ultimaterobotics/uEMG/uEMG_v3/bmi160.h

#include "nrf.h"
#include "nrf_gpio.h"
#include <stdint.h>

typedef struct sBMI160
{
	uint32_t CS;
	float rawA2SI;
	float rawG2SI;
	
	float aX;
	float aY;
	float aZ;

	float wX;
	float wY;
	float wZ;
	
	int16_t raX;
	int16_t raY;
	int16_t raZ;
	
	int16_t rwX;
	int16_t rwY;
	int16_t rwZ;
	
	uint32_t sensor_time;
	
	uint16_t step_cnt;
	
	uint32_t data_id;
	
	uint8_t raw_data[16];

	float G;
	
	float T;
	
	float qW;
	float qX;
	float qY;
	float qZ;
}sBMI160;

void bmi160_init(uint8_t pin_MISO, uint8_t pin_MOSI, uint8_t pin_SCK, uint8_t pin_CS, uint8_t pin_INT);
int bmi160_is_ok();
uint8_t bmi160_read();
void bmi160_enable_dtap();
void bmi160_stop();
void bmi160_resume();

sBMI160 *bmi160_get_data();

int bmi_get_dtap();

void bmi160_normal_mode();

void bmi160_fifo_mode();

void bmi160_acc_mode();
void bmi160_lp_mode();
int bmi_get_tap();

void bmi160_read_steps();
float bmi160_read_temp();

int get_cur_len();
int get_cur_ax(int p);
int get_cur_ay(int p);
int get_cur_az(int p);
